Kalapaja/kampela-hardware/enclosure/new_layout/mass_production/PK 11-196x196x22_1730.sldprt

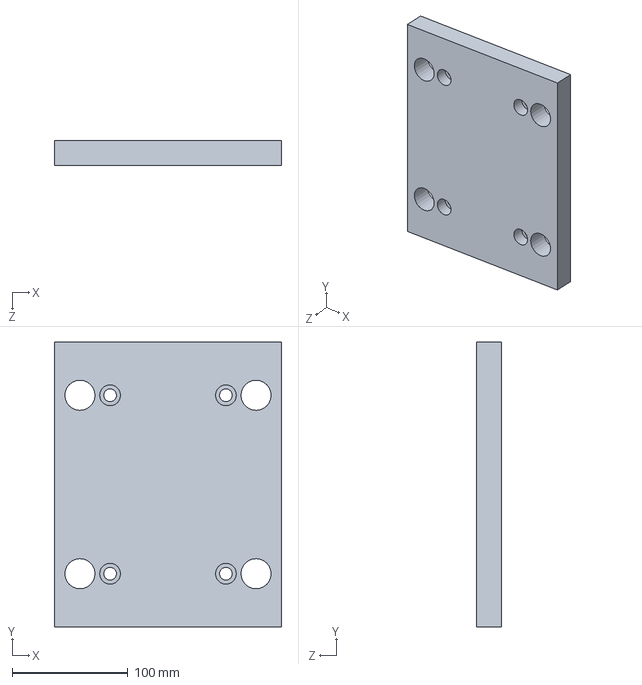
[picture p18: CAD file, 2025-05-06]
enclosure/new_layout/mass_production/PK 11-196x196x22_1730.sldprt
196.0 x 246.0 x 22.0 mm
