Kalapaja/kampela-hardware/enclosure/new_layout/Screen.SLDPRT

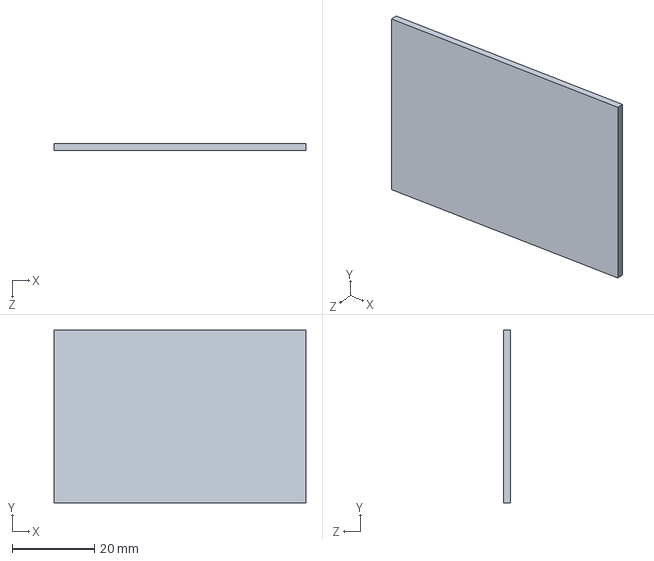
[picture p19: CAD file, 2025-05-06]
enclosure/new_layout/Screen.SLDPRT
61.2 x 42.0 x 1.60 mm
