Kalapaja/kampela-hardware/enclosure/new_layout/Details 3.SLDPRT

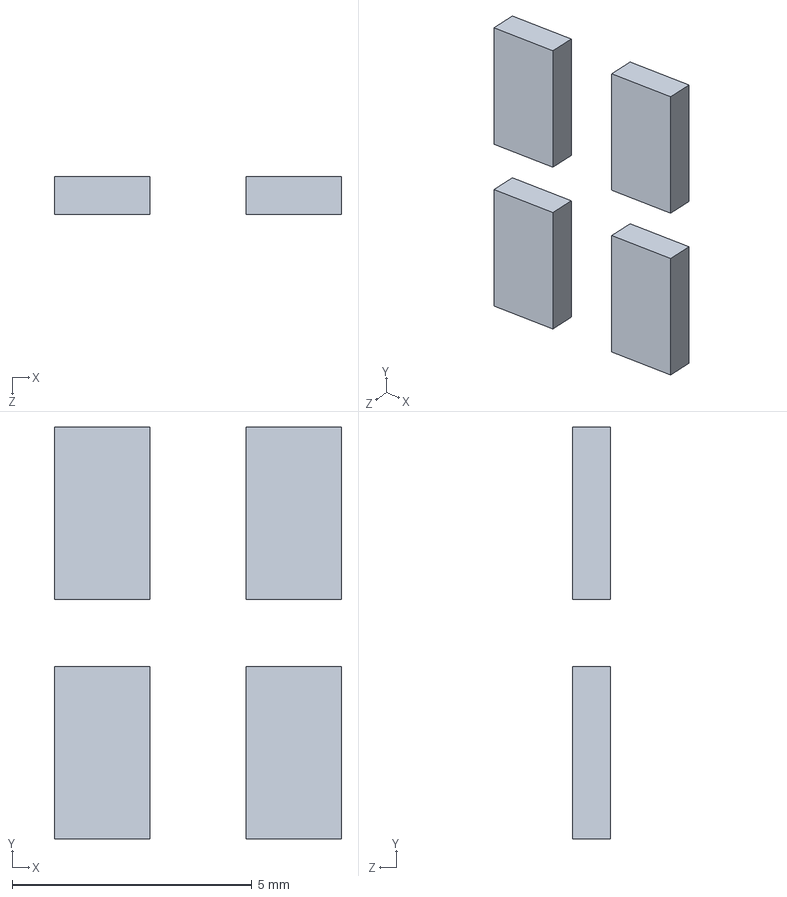
[picture p20: CAD file, 2025-05-06]
enclosure/new_layout/Details 3.SLDPRT
6.00 x 8.60 x 0.8 mm
