Kalapaja/kampela-hardware/enclosure/new_layout/mass_production/TPE-20017.sldprt

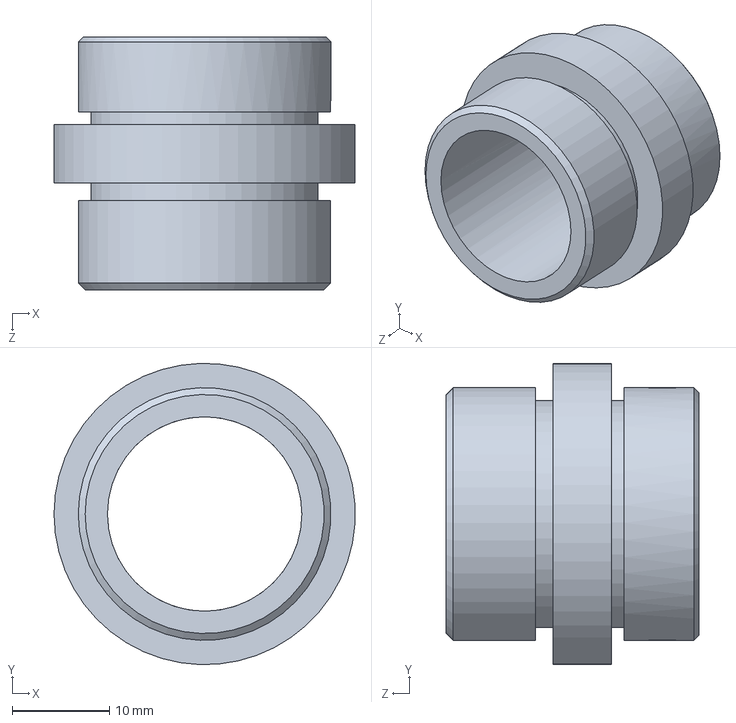
[picture p21: CAD file, 2025-05-06]
enclosure/new_layout/mass_production/TPE-20017.sldprt
31.0 x 31.0 x 26.0 mm
