Kalapaja/kampela-hardware/enclosure/new_layout/mass_production/SM-10080.sldprt

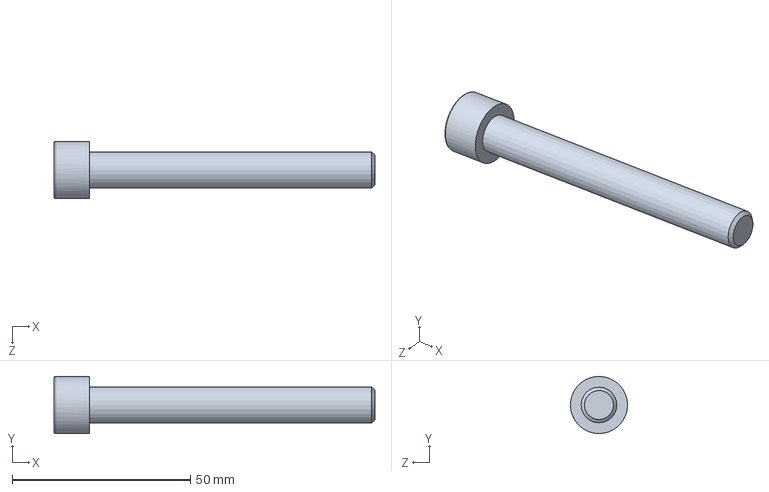
[picture p22: CAD file, 2025-05-06]
enclosure/new_layout/mass_production/SM-10080.sldprt
90.0 x 16.0 x 16.0 mm
