Kalapaja/kampela-hardware/enclosure/new_layout/Mounting.SLDPRT

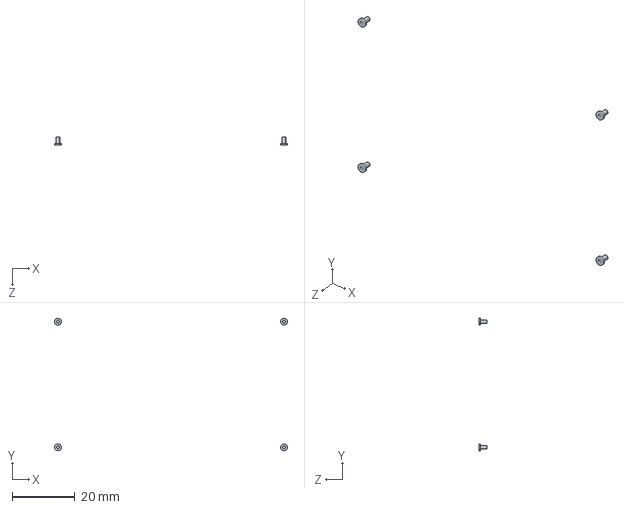
[picture p23: CAD file, 2025-05-06]
enclosure/new_layout/Mounting.SLDPRT
74.2 x 42.2 x 2.50 mm
