Kalapaja/kampela-hardware/enclosure/new_layout/mass_production/PO-1803.sldprt

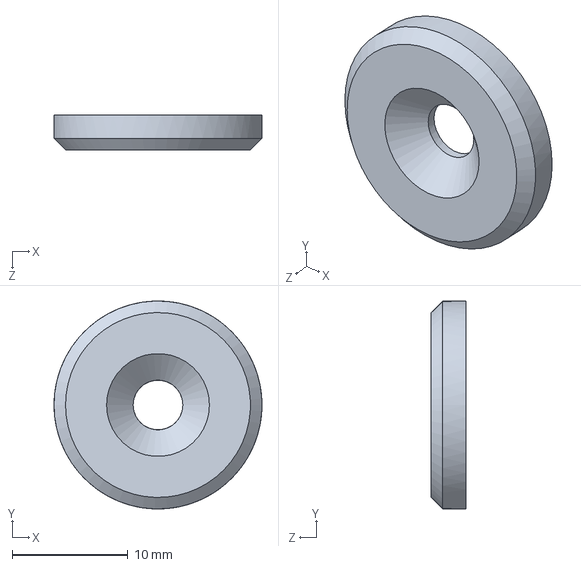
[picture p24: CAD file, 2025-05-06]
enclosure/new_layout/mass_production/PO-1803.sldprt
18.0 x 18.0 x 3.00 mm
