Kalapaja/kampela-hardware/enclosure/new_layout/mass_production/PK 03-196x196x17_1730.sldprt

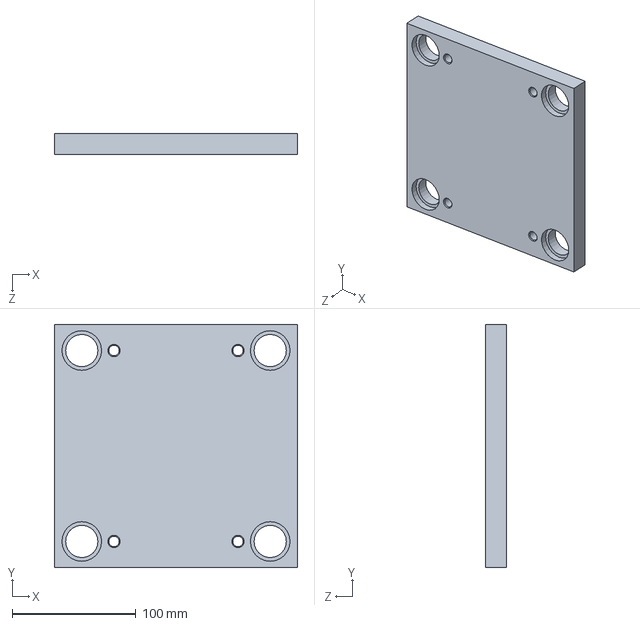
[picture p25: CAD file, 2025-05-06]
enclosure/new_layout/mass_production/PK 03-196x196x17_1730.sldprt
196.0 x 196.0 x 17.0 mm
