Kalapaja/kampela-hardware/enclosure/new_layout/Screen wiring.SLDPRT

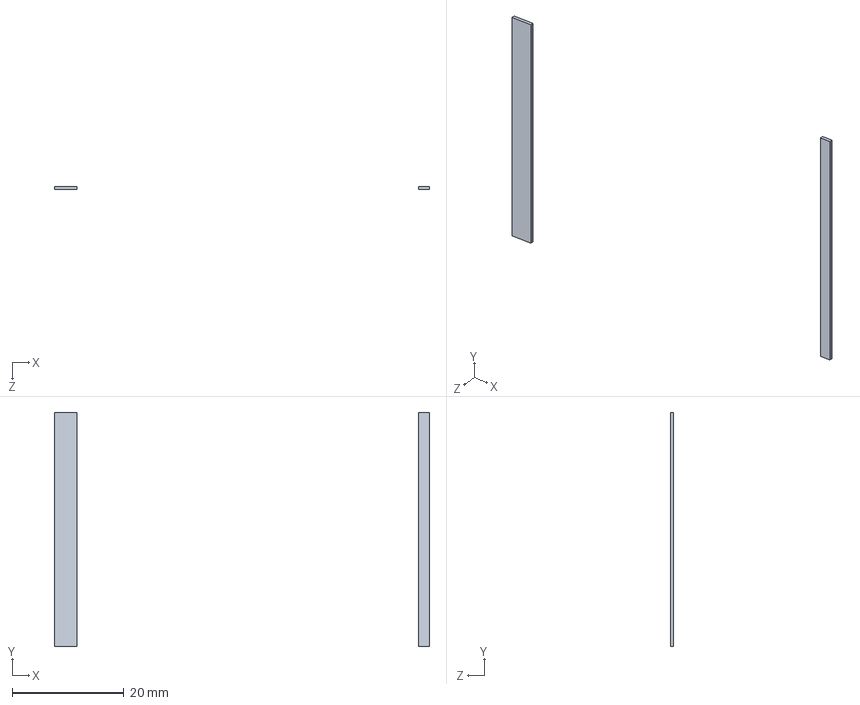
[picture p26: CAD file, 2025-05-06]
enclosure/new_layout/Screen wiring.SLDPRT
67.2 x 42.0 x 0.6 mm
