Kalapaja/kampela-hardware/enclosure/new_layout/NFC.SLDPRT

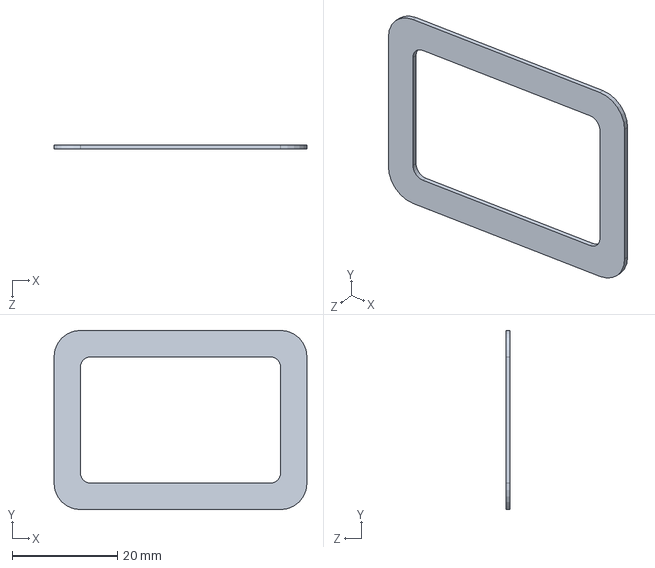
[picture p28: CAD file, 2025-05-06]
enclosure/new_layout/NFC.SLDPRT
48.0 x 34.0 x 0.8 mm
