Kalapaja/kampela-hardware/enclosure/new_layout/mass_production/SM-08016.sldprt

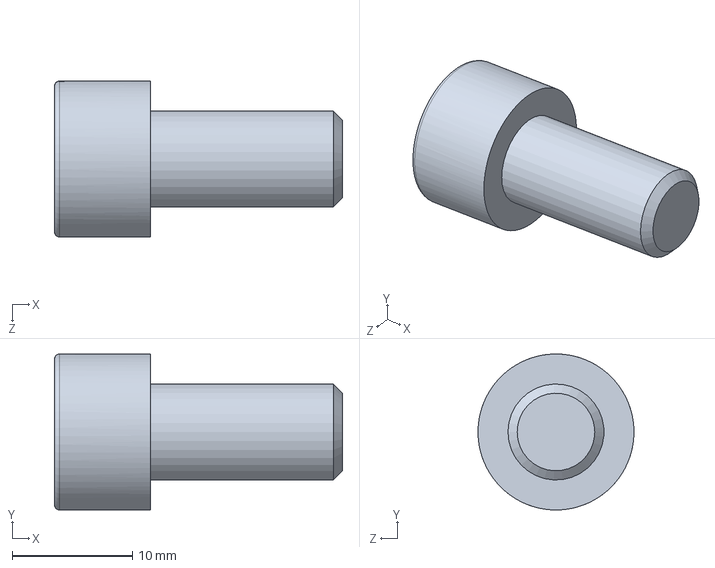
[picture p29: CAD file, 2025-05-06]
enclosure/new_layout/mass_production/SM-08016.sldprt
24.0 x 13.0 x 13.0 mm
