Kalapaja/kampela-hardware/enclosure/new_layout/mass_production/SM-10020.sldprt

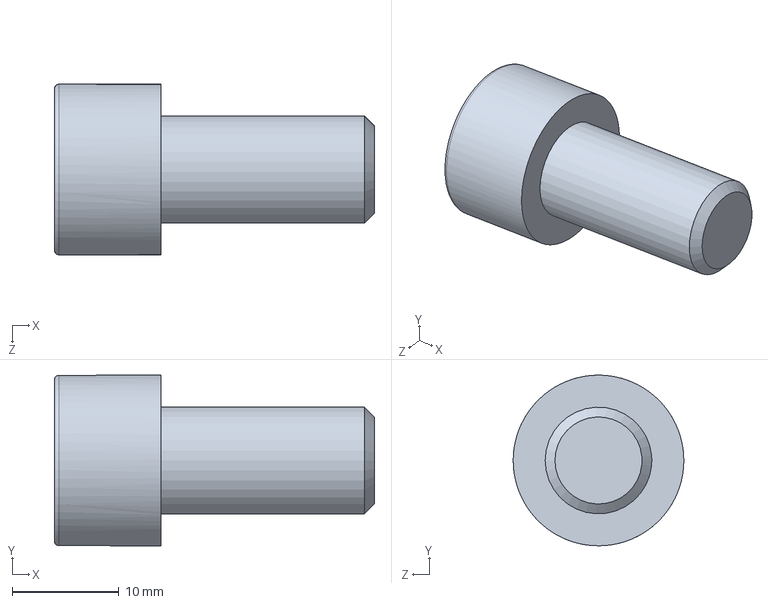
[picture p30: CAD file, 2025-05-06]
enclosure/new_layout/mass_production/SM-10020.sldprt
30.0 x 16.0 x 16.0 mm
