Kalapaja/kampela-hardware/enclosure/new_layout/mass_production/WK-0408.sldprt

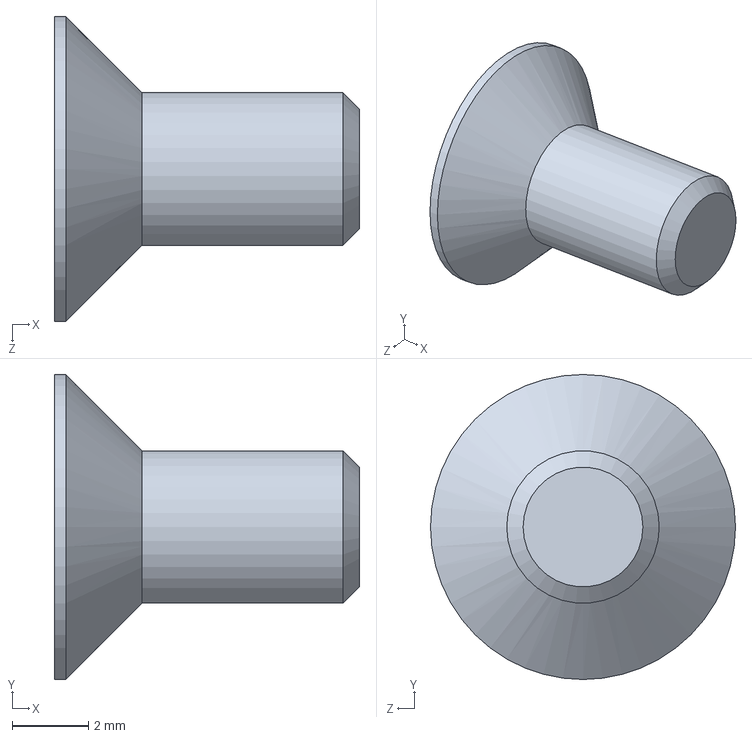
[picture p31: CAD file, 2025-05-06]
enclosure/new_layout/mass_production/WK-0408.sldprt
8.00 x 8.00 x 8.00 mm
