Kalapaja/kampela-hardware/enclosure/new_layout/mass_production/SLE-20017035.sldprt

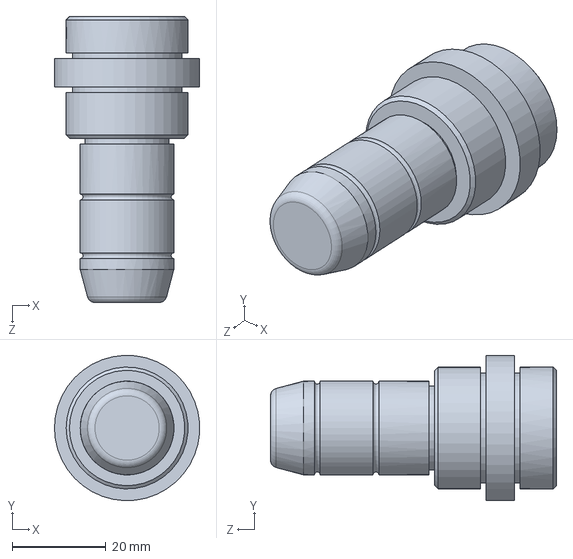
[picture p32: CAD file, 2025-05-06]
enclosure/new_layout/mass_production/SLE-20017035.sldprt
31.0 x 31.0 x 61.0 mm
